GliderWinchItems/BMS/bmsadbms1818/docs/descriptions/header_layout.odt

Note: White bar beside header pin is the GND pin.

1. 4 pin keyed: FAN

2. 3 pin: external LED

3. 2x2: Two spare ADC or I/o

4. 3 pin keyed Molex: DUMP2 FET

5: 4 pin: I2C (gnd,+5, I2C2: SCK, SDA)

6. 6 pin: FTDI (GND, RX, TX)

7. 3 pin: SWD: ST-LINK

8. 2 pin: charger, voltage across 1 ohm

9. 2 pin: thermistor #2: GPIO4 (11/2022 fan control)

10. 2 pin: thermistor #3: GPIO3

11. 2 pin: thermistor #1: GPIO2

12. 3 pin: Hall-effect sensor (gnd, signal: GPIO1, +5)

13. 2 pin: Battery powered (pushbutton for manual wakeup)

14. 2 pin keyed Molex: DUMP (source (black), drain (red))

15. Lug: FET drain (to heater resistor)

16. Lug: FET source (ground)

17. 2 pin: power jumper (remove jumper to measure 12v CAN current)

2x5 header: CAN bus: +12v, -12v, CANH, CANL, Master-Reset)

2x10 header: Battery ribbon

Page 2 11/27/22 BMS1818 header location description
