GliderWinchItems/BMS/docs/description/MAX14921_timing_03182202.PDF

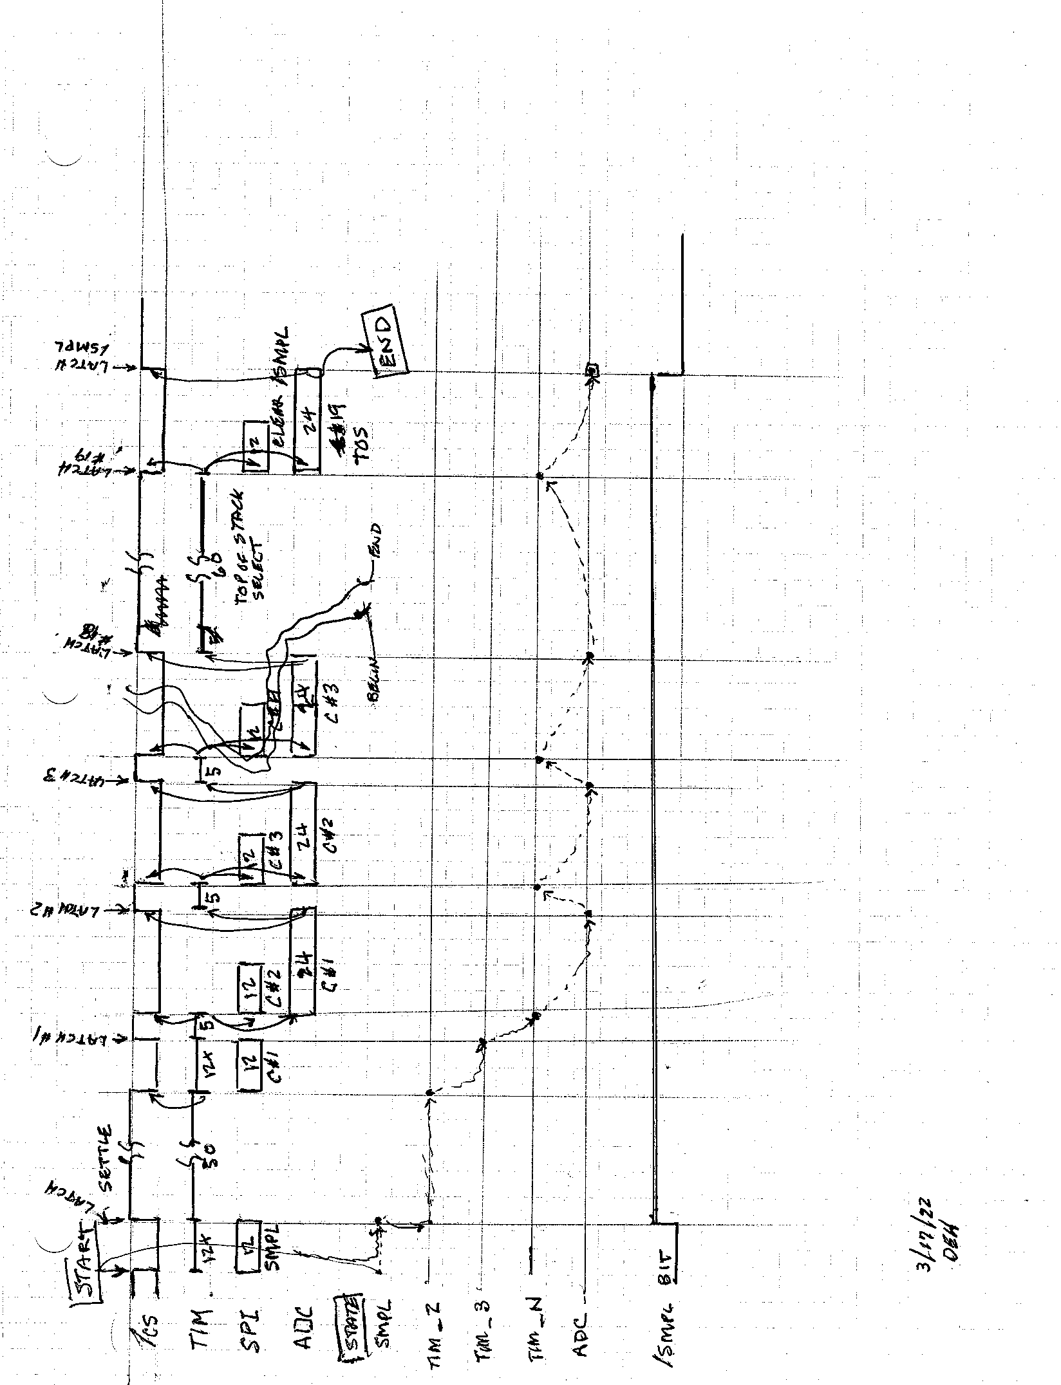
[picture p9: page 1]
