GliderWinchItems/BMS/docs/description/config_02202100.PDF

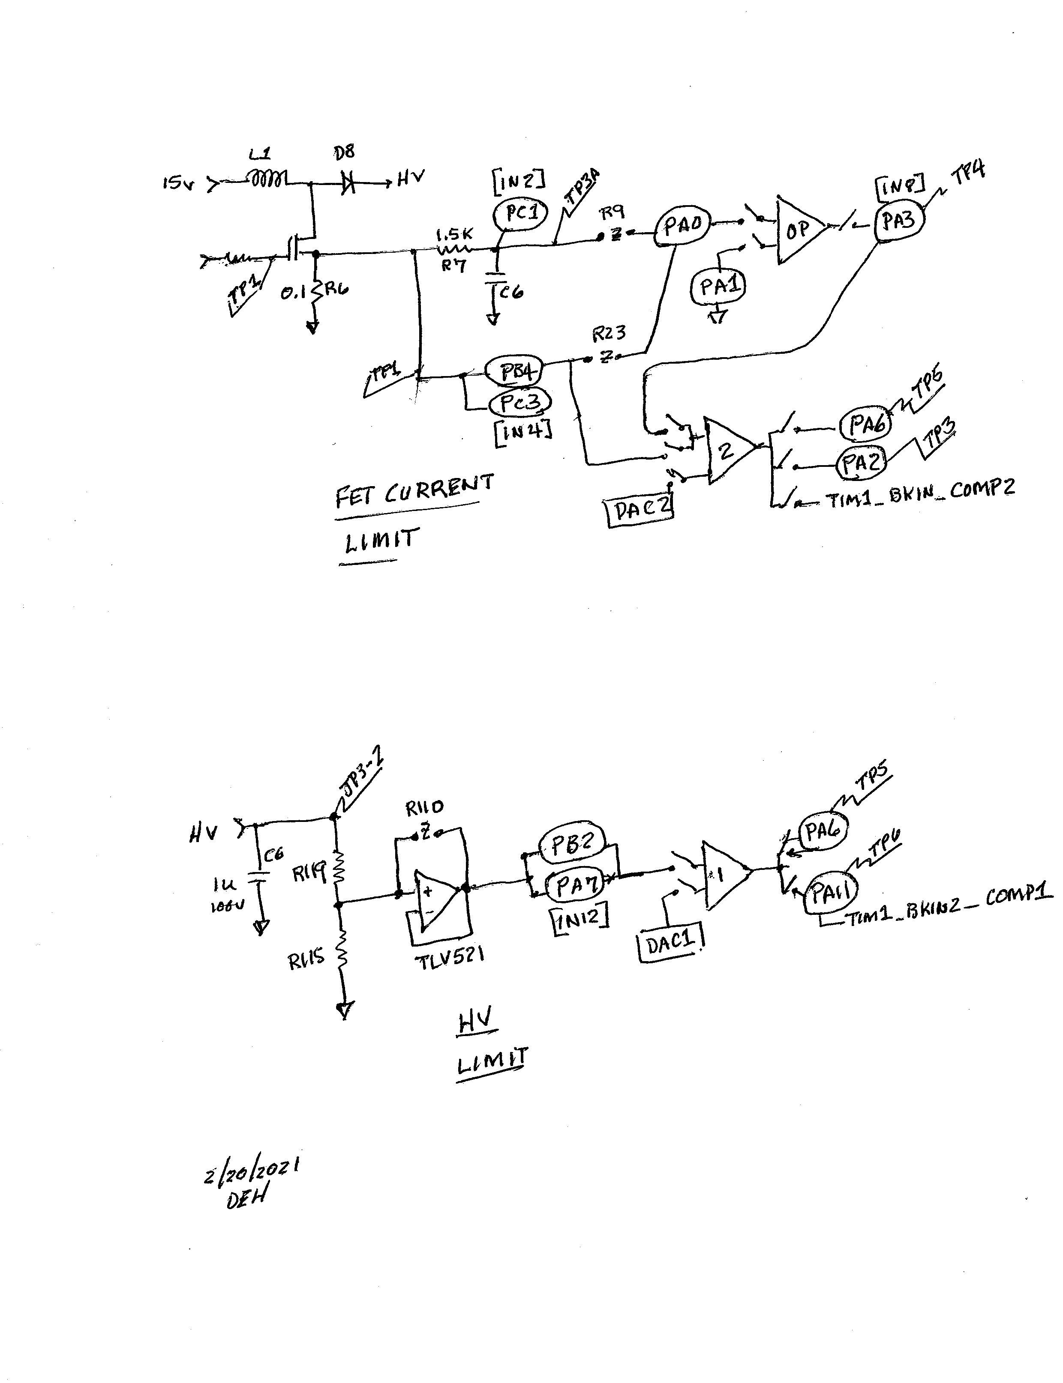
[picture p10: page 1]
