GliderWinchItems/BMS/hw/eagle/bmsbms1818/design_notes.txt

design_notes.txt

06/04/2022

1. Change current sense op amp from GPIO6 to GPIO2

Helps reduce skew for current versus voltage measurements.
See ADCVAX command.

2. '1818 bias resistor 2K-20K.

Use 10K?

08/13/2022

3. Zener vs resistor divider for P-FETs

- Vgs +/- 20v is one solution
- 1M:2M divider
