GliderWinchItems/BMS/LTSpice/BMS_Charger210119.asc

C1: cap; 22µ
C2: cap; 0.1p
C3: cap; 1µ
C4: cap; 6p
D1: schottky; MBRS1100
L1: ind; 47µ; Ipk=2.8 Rser=0.07052 Rpar=4427.4 Cpar=0 mfg="Coilcraft" pn="RFB1010-470"
L2: ind; 1n; Ipk=5 Rser=0.1
M1: nmos; QS8M51_N
R1: res; 500m
R2: res; 50m
R3: res; 10
R4: res; 100m
V1: voltage; 15
V2: voltage; 56
V3: voltage; PULSE(0 5 0 10n 10n 3.4u 7u)
Named nets: 0, Vdrn
.tran 0 224u 210u
