GliderWinchItems/BMS/hw/LTSpice/BMS_Charger.asc

C1: cap; 10µ
C2: cap; 1p
C3: cap; 500n
C4: cap; 18p
D1: schottky; MBRS1100
L1: ind; 39µ; Rser=0.25
L2: ind; 1n; Ipk=5 Rser=0.1
L3: ind; 100n
M1: nmos; QS8M51_N
R1: res; 1
R2: res; 50m
R3: res; 20
R4: res; 100m
R5: res; 5
V1: voltage; 12
V2: voltage; 65
V3: voltage; PULSE(0 5 0 20n 20n 3.5u 5u)
Named nets: 0, Vdrn
.tran 0 100u 75u
