GliderWinchItems/BMS/hw/eagle/Adapt-RJ45to2x5/rj45-2x5.brd

## EAGLE design hw/eagle/Adapt-RJ45to2x5/rj45-2x5.brd (2022-01-06)

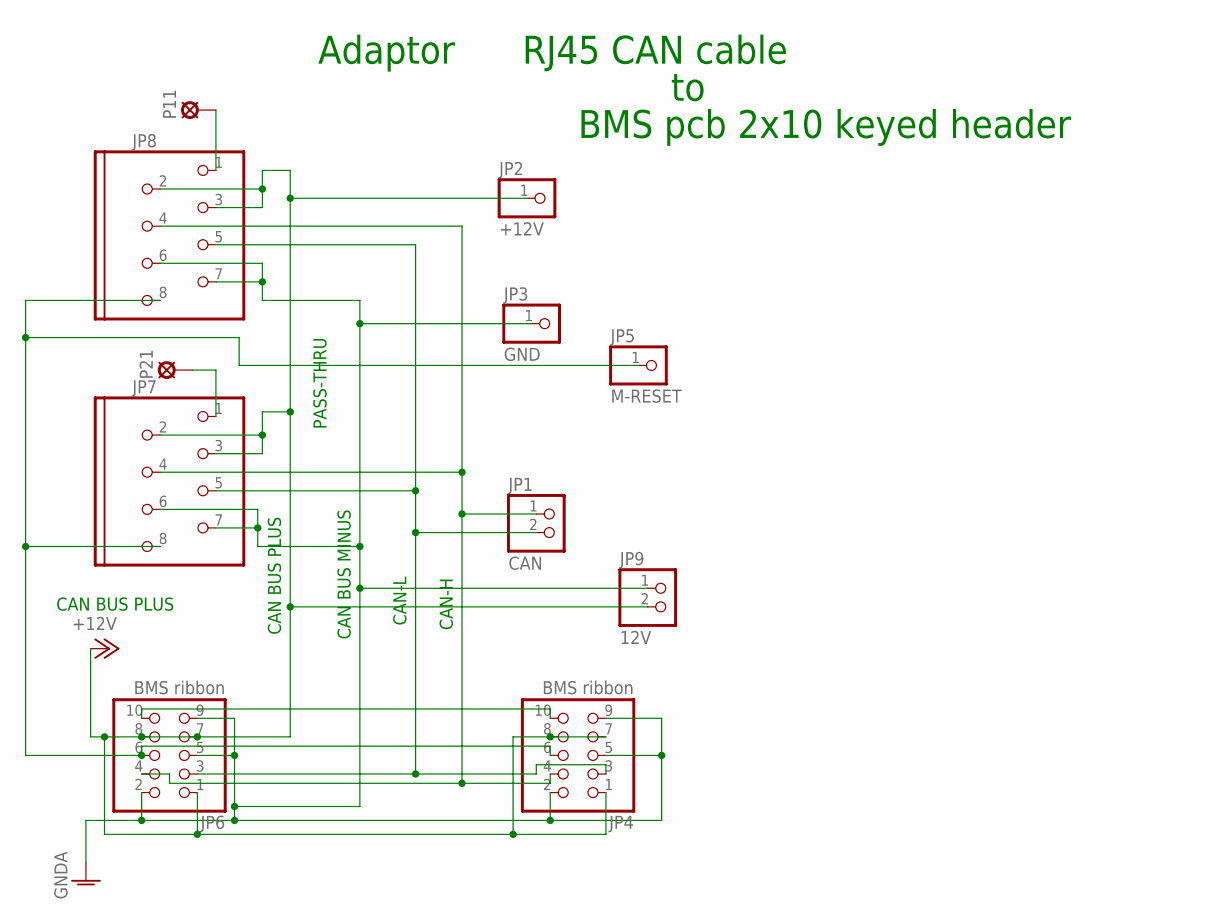
[picture p22: schematic rj45-2x5.sch]

Parts:
JP1: CAN; 1X02
JP2: +12V; 1X01
JP3: GND; 1X01
JP4, JP6: BMS ribbon; 2X05_KEYED
JP5: M-RESET; 1X01
JP7, JP8: MOD8P8C
JP9: 12V; 1X02
P11, P21: SOLPAD035; SOLDPAD035

Connections:
+12V: JP2.1, JP4.1, JP4.7, JP4.8, JP6.1, JP6.7, JP6.8, JP7.2 (5), JP7.3 (2), JP8.2 (5), JP8.3 (2), JP9.2
CANCABLE_1_1: JP8.1, P11.MP
CANCABLE_2_1: JP7.1, P21.MP
CANH: JP1.1, JP4.4, JP6.4, JP7.4 (6), JP8.4 (6)
CANL: JP1.2, JP4.3, JP6.3, JP7.5 (3), JP8.5 (3)
GNDA: JP3.1, JP4.2, JP4.5, JP4.9, JP6.2, JP6.5, JP6.9, JP7.6 (7), JP7.7 (4), JP8.6 (7), JP8.7 (4), JP9.1
MASTER-RESET-SYS: JP4.6, JP5.1, JP6.6, JP7.8, JP8.8
unnamed: JP4.10, JP6.10

Notes on the sheet:
CAN BUS PLUS
PASS-THRU
CAN BUS MINUS
CAN-H
CAN-L
Adaptor
RJ45 CAN cable
BMS pcb 2x10 keyed header

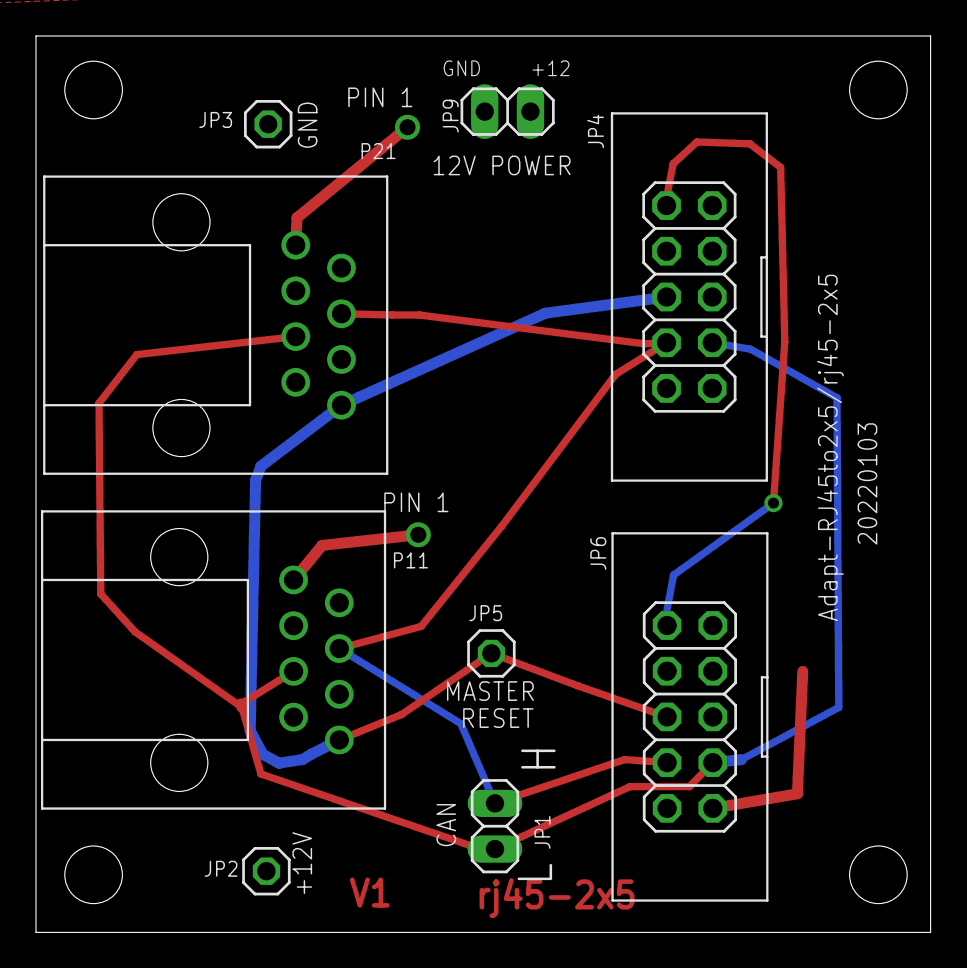
[picture p23: board rj45-2x5.brd from above]

Board: 2 copper layers, 49.7 x 49.8 mm, 11 parts (0 on the bottom side), 8 nets.
