GliderWinchItems/BMS/hw/eagle/rj45-2x10/rj45-2x10.brd

## EAGLE design hw/eagle/rj45-2x10/rj45-2x10.brd (2021-09-04)

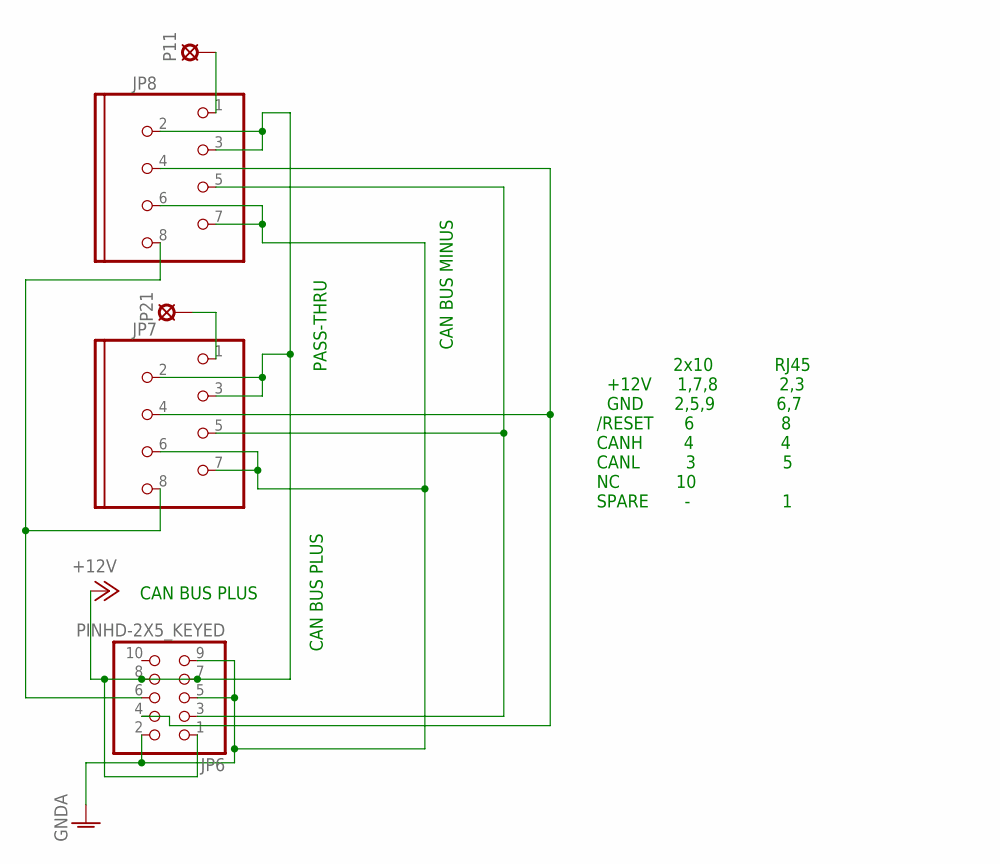
[picture p24: schematic rj45-2x10.sch]

Parts:
JP6: PINHD-2X5_KEYED; 2X05_KEYED
JP7, JP8: MOD8P8C
P11, P21: SOLPAD035; SOLDPAD035

Connections:
+12V: JP6.1, JP6.7, JP6.8, JP7.2 (5), JP7.3 (2), JP8.2 (5), JP8.3 (2)
CANCABLE_1_1: JP8.1, P11.MP
CANCABLE_2_1: JP7.1, P21.MP
CANH: JP6.4, JP7.4 (6), JP8.4 (6)
CANL: JP6.3, JP7.5 (3), JP8.5 (3)
GNDA: JP6.2, JP6.5, JP6.9, JP7.6 (7), JP7.7 (4), JP8.6 (7), JP8.7 (4)
MASTER-RESET-SYS: JP6.6, JP7.8, JP8.8

Notes on the sheet:
CAN BUS PLUS
PASS-THRU
CAN BUS MINUS
2x10 RJ45 +12V 1,7,8 2,3 GND 2,5,9 6,7 /RESET 6 8 CANH 4 4 CANL 3 5 NC 10 SPARE - 1

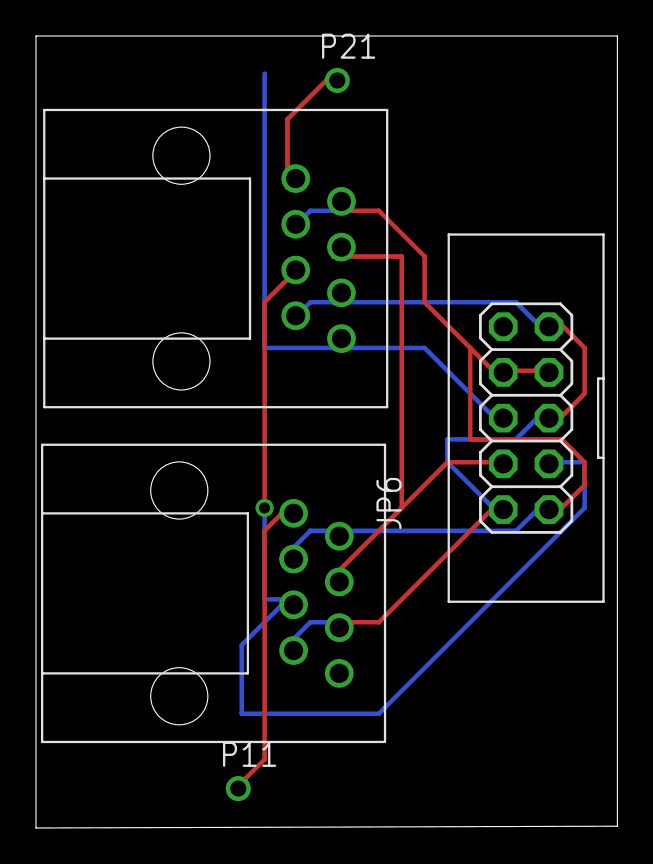
[picture p25: board rj45-2x10.brd from above]

Board: 2 copper layers, 32.3 x 44.0 mm, 5 parts (0 on the bottom side), 7 nets.
