GliderWinchItems/BMS/bmsadbms1818/Core/Inc/main.h

#define RTC_BAT_PWR_Pin GPIO_PIN_13
#define RTC_BAT_PWR_GPIO_Port GPIOC
#define FET_CUR_A2_Pin GPIO_PIN_3
#define FET_CUR_A2_GPIO_Port GPIOC
#define OPAMP_INP_Pin GPIO_PIN_0
#define OPAMP_INP_GPIO_Port GPIOA
#define OPAMP_INM_Pin GPIO_PIN_1
#define OPAMP_INM_GPIO_Port GPIOA
#define OPAMP_OUT_Pin GPIO_PIN_3
#define OPAMP_OUT_GPIO_Port GPIOA
#define dc_dc_15V_Pin GPIO_PIN_4
#define dc_dc_15V_GPIO_Port GPIOA
#define FAN_PWM_Pin GPIO_PIN_5
#define FAN_PWM_GPIO_Port GPIOA
#define HV_div1_Pin GPIO_PIN_7
#define HV_div1_GPIO_Port GPIOA
#define LED_GRN_Pin GPIO_PIN_0
#define LED_GRN_GPIO_Port GPIOB
#define LED_RED_Pin GPIO_PIN_1
#define LED_RED_GPIO_Port GPIOB
#define HV_div2_Pin GPIO_PIN_2
#define HV_div2_GPIO_Port GPIOB
#define FANTach_Pin GPIO_PIN_10
#define FANTach_GPIO_Port GPIOB
#define PADxx_Pin GPIO_PIN_12
#define PADxx_GPIO_Port GPIOB
#define PAD7_Pin GPIO_PIN_15
#define PAD7_GPIO_Port GPIOB
#define DUMP2_Pin GPIO_PIN_6
#define DUMP2_GPIO_Port GPIOC
#define DUMP_NOT_Pin GPIO_PIN_8
#define DUMP_NOT_GPIO_Port GPIOC
#define CSB_Pin GPIO_PIN_15
#define CSB_GPIO_Port GPIOA
#define DUMP_Pin GPIO_PIN_10
#define DUMP_GPIO_Port GPIOC
#define HEATER_NOT_Pin GPIO_PIN_11
#define HEATER_NOT_GPIO_Port GPIOC
#define HEATER_Pin GPIO_PIN_12
#define HEATER_GPIO_Port GPIOC
#define BQ_LD_Pin GPIO_PIN_2
#define BQ_LD_GPIO_Port GPIOD
#define WDT_Pin GPIO_PIN_7
#define WDT_GPIO_Port GPIOB
#define WDT_EXTI_IRQn EXTI9_5_IRQn
#define HUARTMON  huart1 // uart  for PC monitoring
#define DEFAULTTASKBIT00 (1 << 0)  // Task notification bit (from ADCtask.c)
#define DEFAULTTASKBIT01 (1 << 1)  // Task notification bit (from BQtask.c)
#define DEFAULTTASKBIT02 (1 << 2)  // Task notification bit (from Mailbox)
#define MAINFORLOOPDELAY 50 // main.c Delay of 'for' loop (ms)
