GliderWinchItems/BMS/bmsmax14921/Ourtasks/CanCommTask.c

/******************************************************************************
* File Name          : CanCommTask.c
* Date First Issued  : 11/06/2021
* Description        : Can communications
*******************************************************************************/

#include "FreeRTOS.h"
#include "task.h"
#include "cmsis_os.h"
#include "malloc.h"

#include "main.h"
#include "morse.h"
#include "CanCommTask.h"
#include "MailboxTask.h"
#include "CanTask.h"
#include "can_iface.h"
#include "canfilter_setup.h"
#include "BQTask.h"
#include "cancomm_items.h"
#include "../../../../GliderWinchCommons/embed/svn_common/trunk/db/gen_db.h"

extern struct CAN_CTLBLOCK* pctl0; // Pointer to CAN1 control block
extern CAN_HandleTypeDef hcan1;

static void canfilt(uint16_t mm, struct MAILBOXCAN* p);

#define CANCOMMBIT00 (1 << 0) // Send cell voltage  command
#define CANCOMMBIT01 (1 << 1) // Send misc reading command
#define CANCOMMBIT02 (1 << 2) // Multi-purpose incoming command
#define CANCOMMBIT03 (1 << 3) // ADCTask completed BMS read 

struct CANRCVBUF  can_hb; // Dummy heart-beat request CAN msg
uint8_t hbseq; // heartbeat CAN msg sequence number
uint8_t rdyflag_cancomm = 0; // Initialization complete and ready = 1

TaskHandle_t CanCommHandle = NULL;

static struct ADCREADREQ adcreadreq; // Request BMS readout

uint8_t dbupdnx;

/* Walking discharge FETs for testing. */
uint16_t dbdischargectr; // hb counter for timing
uint8_t  dbdischargebit; // Discharge bit (0-15)

/* Arrays loaded by readbms. */
float fbms[ADCBMSMAX]; // (16+3+1) = 20; Number of MAX14921 (cells+thermistors+tos)   
uint16_t uibms[ADCBMSMAX];

/* *************************************************************************
 * void CanComm_init(struct BQFUNCTION* p );
 *	@brief	: Task startup
 * *************************************************************************/
void CanComm_init(struct BQFUNCTION* p )
{
	uint8_t i;

	/* Add CAN Mailboxes                               CAN     CAN ID             TaskHandle,Notify bit,Skip, Paytype */
    p->pmbx_cid_cmd_bms_cellvq = MailboxTask_add(pctl0,p->lc.cid_cmd_bms_cellvq, NULL, CANCOMMBIT00,0,U8); // Command: send cell voltages
    if (p->pmbx_cid_cmd_bms_cellvq == NULL) morse_trap(620);
    p->pmbx_cid_cmd_bms_miscq  = MailboxTask_add(pctl0,p->lc.cid_cmd_bms_miscq,  NULL, CANCOMMBIT01,0,U8); // Command: many options	
    if (p->pmbx_cid_cmd_bms_miscq == NULL) morse_trap(621);
    p->pmbx_cid_uni_bms_i      = MailboxTask_add(pctl0,p->lc.cid_uni_bms_i,      NULL, CANCOMMBIT02,0,U8); // muli-purpose BQ76952  #01
    if (p->pmbx_cid_uni_bms_i == NULL) morse_trap(622);

    /* Add CAN msgs to incoming CAN filter. */
 //   canfilt(601, p->pmbx_cid_cmd_bms_cellvq);
 //   canfilt(602, p->pmbx_cid_cmd_bms_miscq);
 //   canfilt(603, p->pmbx_cid_uni_bms_i);

    	/* Pre-load fixed data in all possible CAN msgs */
	for (i = 0; i < NUMCANMSGS; i++)
	{
		p->canmsg[i].pctl = pctl0;   // Control block for CAN module (CAN 1)
		p->canmsg[i].maxretryct = 4; //
		p->canmsg[i].bits = 0;       //
		p->canmsg[i].can.dlc = 8;    // Default payload size (might be modified when loaded and sent)
	}

	/* Preload fixed data for sending cell reading msgs. */
	for (i = 0; i < MAXNUMCELLMSGS; i++)
	{	
		/* Preload CAN IDs */
		p->canmsg[CID_MSG_CELLV01 + i].can.id = p->lc.cid_msg_bms_cellvsmr;

		/* Msg identification = cell readings. */
		p->canmsg[CID_MSG_CELLV01 + i].can.cd.ui[0]  = CMD_CMD_TYPE1;//

		/* Preload cell_number-1 for first payload in cell reading msg. */
		// 0,3,6,9,12,15 in upper nibble; lower order nibble (seq number) = 0;
		p->canmsg[CID_MSG_CELLV01 + i].can.cd.ui[1] = ((i*3) << 4); 
	}

	/* Preload fixed data for sending "misc" readings. */
	p->canmsg[CID_CMD_MISC].can.id = p->lc.cid_msg_bms_cellvsmr;
	p->canmsg[CID_CMD_MISC].can.cd.uc[2] = p->ident_onlyus;

	/* Pre-load a dummy CAN msg request for sending heartbeat CAN msg. */
	can_hb.id       = p->lc.cid_uni_bms_i;
	can_hb.cd.ull   = 0; // Clear entire payload
	can_hb.cd.uc[0] = CMD_CMD_TYPE1;  // request code (initial, changed later)
	can_hb.cd.uc[4] = p->lc.cid_msg_bms_cellvsmr >>  0; // Our CAN ID
	can_hb.cd.uc[5] = p->lc.cid_msg_bms_cellvsmr >>  8;
	can_hb.cd.uc[6] = p->lc.cid_msg_bms_cellvsmr >> 16;
	can_hb.cd.uc[7] = p->lc.cid_msg_bms_cellvsmr >> 24;

	return;
}

/* *************************************************************************
 * void StartCanComm(void const * argument);
 *	@brief	: Task startup
 * *************************************************************************/
void StartCanComm(void* argument)
{
//while(1==1) osDelay(100);

	BaseType_t qret;
	uint32_t noteval2;
	struct ADCREADREQ* padcreadreq = &adcreadreq;

	/* We use the parameters from BQ for this task. */
	struct BQFUNCTION* p = &bqfunction;
	struct CANRCVBUF* pcan;

	uint32_t doneflagctr;

	/* A notification copies the internal notification word to this. */
	uint32_t noteval = 0;    // Receives notification word upon an API notify
	uint32_t timeoutwait;
	uint8_t intadj = 0;
	uint8_t code;

//	while (CANTaskreadyflag == 0) osDelay(1); // Debug

	/* Pre-load BMS readout request queue block. */	
//	adcreadreq.taskhandle = CanCommHandle; // Requesting task's handle
//	adcreadreq.tasknote   = CANCOMMBIT03;  // ADCTask completed BMS read 
	adcreadreq.taskdata   = &fbms[0];  // Requesting task's pointer to buffer to receive data
	adcreadreq.taskdatai16= &uibms[0]; // Requesting task's pointer to int16_t buffer to receive data
	adcreadreq.cellbits   = 0x0000;    // Depends on command: FET to set; Open cell wires
	adcreadreq.updn       = 0; // BMS readout direction 0 = high->low cell numbers; 1 = low->high
	adcreadreq.reqcode    = REQ_READBMS;  // Read MAX1921 cells, thermistor, Top-of-stack
	adcreadreq.encycle    = 1;     // Cycle EN: 0 = after read; 1 = before read w osDelay; 2 = neither
	adcreadreq.readbmsfets= 0;        // Clear discharge fets before readbms.	
	adcreadreq.doneflag   = 0; // 1 = ADCTask completed BMS read 
dbupdnx = adcreadreq.updn;

	/* CAN communications parameter init. */
	CanComm_init(p);

	extern CAN_HandleTypeDef hcan1;
	HAL_CAN_Start(&hcan1); // CAN1

	rdyflag_cancomm = 1; // Initialization complete and ready
/* ******************************************************************* */
	for (;;)
	{
		/* Wait for notifications */
		/* Do exactly 12 timeouts per second. */
		intadj += 1;
		if (intadj >= 3)
		{
			timeoutwait = 84;
			intadj = 0;
		}
		else
		{
			timeoutwait = 83;
		}
//timeoutwait = 40;

		xTaskNotifyWait(0,0xffffffff, &noteval,timeoutwait);

		/* Read BMS cells. */
		adcreadreq.doneflag   = 0;
		doneflagctr = 0;

		qret = xQueueSendToBack(ADCTaskReadReqQHandle, &padcreadreq, 5000);
if (qret != pdPASS) morse_trap(720); // JIC debug

		/* Wait for ADCTask to complete request. */
#define DONEFLAGCT 200
		while ((adcreadreq.doneflag == 0) && (doneflagctr++ < DONEFLAGCT)) 
			osDelay(1);
		if (doneflagctr >= DONEFLAGCT) morse_trap(731);


		/* Filter readings for calibration purposes. */
		cancomm_items_filter(pssb->taskdatai16); // Filter 	

/* ******* CAN msg request for sending CELL VOLTAGES. */
			// Code for which modules should respond bits [7:6]
	   		// 11 = All modules respond
       		// 10 = All modules on identified string respond
       		// 01 = Only identified string and module responds
       		// 00 = spare; no response expected
		if ((noteval & CANCOMMBIT00) != 0) // cid_cmd_bms_cellvq
		{
morse_trap(6666);			
			pcan = &p->pmbx_cid_cmd_bms_cellvq->ncan.can;
			code = pcan->cd.uc[0] & 0xC0; // Extract identification code
			if (((code == (3 << 6))) ||
				((code == (2 << 6)) && ((pcan->cd.uc[0] & 0x30) == p->ident_string)) ||
				((code == (1 << 6)) && ((pcan->cd.uc[0] & 0x3F) == p->ident_onlyus)) )
			{ // Here, respond to request, otherwise, ignore.
				qret = xQueueSendToBack(ADCTaskReadReqQHandle, &padcreadreq, 5000);
				if (qret != pdPASS) morse_trap(726); // JIC debug

				/* Wait for ADCTask to signal request complete. */
				xTaskNotifyWait(0,0xffffffff, &noteval2, 5000);
				if (noteval2 != CANCOMMBIT03) morse_trap(727); // JIC debug

				cancomm_items_uni_bms(&can_hb, &fbms[0]);
			}
		}
/* ******* CAN msg request for sending MISC READINGS. */
			// Code for which modules should respond bits [7:6]
	   		// 11 = All modules respond
       		// 10 = All modules on identified string respond
       		// 01 = Only identified string and module responds
       		// 00 = spare; no response expected
		if ((noteval & CANCOMMBIT01) != 0) // cid_cmd_bms_miscq
		{
morse_trap(5555);
			pcan = &p->pmbx_cid_cmd_bms_miscq->ncan.can;
			code = pcan->cd.uc[0] & 0xC0; // Extract identification code
			if (((code == (3 << 6))) ||
				((code == (2 << 6)) && ((pcan->cd.uc[0] & 0x30) == p->ident_string)) ||
				((code == (1 << 6)) && ((pcan->cd.uc[0] & 0x3F) == p->ident_onlyus)) )
			{ // Here, respond to request
				cancomm_items_sendcmdr(pcan);
			}
		}
/* ******* CAN msg request for sending MISC READINGS. */
		if ((noteval & CANCOMMBIT02) != 0) // cid_uni_bms_i
		{
bqfunction.CanComm_hb_ctr = 0;			
			cancomm_items_uni_bms(&p->pmbx_cid_uni_bms_i->ncan.can, NULL);
		}

/* ******* Timeout notification. */
		if (noteval == 0)
		{ // Send heartbeat

#if 0 /* Walk discharge FETs for testing. */
			dbdischargectr += 1; // Time delay counter
			if (dbdischargectr >= 32)
			{ // Set FETs off
				adcreadreq.cellbits = 0;
			}
			if (dbdischargectr >= 64)
			{ // Step to next FET
				dbdischargectr = 0;
				dbdischargebit += 1;
				if (dbdischargebit >= 16) dbdischargebit = 0;
			}
#endif
			/* Here, 12 times per second. Slow down for heartbeat. */
			bqfunction.CanComm_hb_ctr += 1;
			if (bqfunction.CanComm_hb_ctr >= bqfunction.lc.CanComm_hb)
			{
				bqfunction.CanComm_hb_ctr = 0;

				/* Use dummy CAN msg, then it looks the same as a request CAN msg. */
				can_hb.cd.uc[0] = CMD_CMD_TYPE2;  // Misc subcommands code
				can_hb.cd.uc[1] = MISCQ_STATUS;   // status code
				cancomm_items_uni_bms(&can_hb,&bqfunction.cal_filt[0]); // filtered

				/* Use dummy CAN msg, then it looks the same as a request CAN msg. */
				can_hb.cd.uc[0] = CMD_CMD_TYPE1;  // cell readings code
				can_hb.cd.uc[1] = (hbseq & 0x0f); // Group sequence number
				cancomm_items_uni_bms(&can_hb, &bqfunction.cal_filt[0]); // filtered

				/* Increment 4 bit CAN msg group sequence counter .*/
				hbseq += 1;
//	   			xQueueSendToBack(CanTxQHandle,&p->canmsg[CID_CMD_MISC],4);   
   			}
		}	
	} 	
}

/* *************************************************************************
 * TaskHandle_t xCanCommCreate(uint32_t taskpriority);
 * @brief	: Create task; task handle created is global for all to enjoy!
 * @param	: taskpriority = Task priority (just as it says!)
 * @return	: CanCommHandle
 * *************************************************************************/
TaskHandle_t xCanCommCreate(uint32_t taskpriority)
{
	BaseType_t ret = xTaskCreate(StartCanComm, "CanComm",\
     (128), NULL, taskpriority,\
     &CanCommHandle);
	if (ret != pdPASS) return NULL;

	return CanCommHandle;
}
/* *************************************************************************
 * static void canfilt(uint16_t mm, struct MAILBOXCAN* p);
 * @brief	: Setup CAN hardware filter with CAN addresses to receive
 * @param	: p    = pointer to ContactorTask
 * @param   : mm = morse_trap numeric number
 * *************************************************************************/
static void canfilt(uint16_t mm, struct MAILBOXCAN* p)
{
/*	HAL_StatusTypeDef canfilter_setup_add32b_id(uint8_t cannum, CAN_HandleTypeDef *phcan, \
    uint32_t id,   \
    uint8_t  fifo );
 @brief	: Add a 32b id, advance bank number & odd/even
 * @param	: cannum = CAN module number 1, 2, or 3
 * @param	: phcan = Pointer to HAL CAN handle (control block)
 * @param	: id    = 32b CAN id
 * @param	: fifo  = fifo: 0 or 1
 * @return	: HAL_ERROR or HAL_OK
*/
	HAL_StatusTypeDef ret;	
	ret = canfilter_setup_add32b_id(1,&hcan1,p->ncan.can.id,0);
	if (ret == HAL_ERROR) morse_trap(mm);	
	return;
}
