GliderWinchItems/BMS/bmsadbms1818/params/B0A00000-bq_idx_v_struct.c

/******************************************************************************
* File Name          : B0A00000-bq_idx_v_struct.c
* Date First Issued  : 08/20/2022
* Board              : bmsadbms1818
* Description        : Load BQ parameter struct: B0A00000 ADBMS1818 board #1
*******************************************************************************/
/*
16 pin CAN ISO1042
*/

#include "bq_idx_v_struct.h"
#include "SerialTaskReceive.h"
#include "morse.h"
#include "../../../../GliderWinchCommons/embed/svn_common/trunk/db/gen_db.h"

/* *************************************************************************
 * void bq_idx_v_struct_hardcode_params(truct BQLC* p);
 * @brief	: Init struct from hard-coded parameters (rather than database params in highflash)
 * @return	: 0
 * *************************************************************************/
void bq_idx_v_struct_hardcode_params(struct BQLC* p)
{
   p->size    = 32;
   p->crc     = 0;   // TBD
   p->version = 1;   // 

   /* Timings in milliseconds. Converted later to timer ticks. */

   /* Identification of this module node. */
   p->winchnum     = 1; // Winch number (1 - 4)
   if ((p->winchnum == 0) || (p->winchnum > 4)) morse_trap(700);
   p->stringnum    = 1; // Battery string number (1 - 4)
   if ((p->stringnum == 0) || (p->stringnum > 4)) morse_trap(701);
   p->modulenum    = 2; // Module number on string (1-16)
   if ((p->modulenum == 0) || (p->modulenum > 16)) morse_trap(702);

   p->hbct_t       = 4000; // Heartbeat ct: milliseconds between sending 
   p->hbct         = 64;    // Number of swctr ticks between heartbeats
//   p->adc_hb       = 64;     // Number of ticks for heartbeat ADC readout

   p->CanComm_hb = 1000; // CanCommTask 'wait' RTOS ticks per heartbeat sending
 
   p->dcdc_v    = 15.0; // Isolated DC-DC converter output voltage (e.g. 15.0v)
   p->dcdc_w    =  5.2; // Charger power max taken from DC-DC converter (e.g. 5.5W)
   p->dcdc_calv = 68.5; // Module voltage used in following settings (e.g. 57.6v)

   /* Charger: timer and comparator settings. */
   p->dac1_hv_setting  = 3900; // HV volt limit (DAC setting, not mv!)
   p->dac2_ix_setting  =   85; // Current sense level setting (DAC setting)
   p->tim1_ccr1_on     =  999; // PWM ON count: Normal charge rate
   p->tim1_ccr1_on_vlc =   10; // PWM ON count: Very Low Charge rate required
   p->tim1_arr_init    =   25; // At 16 MHz: count of 80 = 5 us PWM frame

   p->cellv_max      = 3750; // Max limit (mv) for charging any cell
   p->cellv_min      = 2800; // Min limit (mv) for any discharging
   p->cellv_vlc      = 2100; // Below this (mv) Very Low Charge (vlc)required
   p->cellv_tgtdelta =    3; // Target delta (mv)   
   p->cellopen_hi    = 4000; // Above this voltage cell wire is assumed open (mv)
   p->cellopen_lo    =  333; // Below this voltage cell wire is assumed open (mv)
   p->cellv_max2_inc =  100; // Increment added to cellv_max for external charging

   p->balnummax    = 18;  // Max number of cells to discharge at one time

   // Voltage below cellv_max to start recharging (mv)
   p->cellv_hyster = (p->cellv_max - 3250);  // 3250 LFP ~50% charge

   p->dumpresistor = 450; // DUMP fet load resistor (Ohms)

   /* Future Not implemented (09/13/23) */
   p->cellv_launch_ng  = 3144;  //  Low cell voltage for launch no-go (mv)
   p->cellv_min_loaded = 1800;  //  Low cell voltage too low even under load (mv)

   p->cellbal_del  = 2; // Legacy

  /* Arrays compiled using NCELLMAX [18] */
   p->ncell = 18; // Number of series cells in this module
   if (p->ncell > NCELLMAX) morse_trap(702); // Error trap as it needs fixing
   p->npositions  = 18;  // Number of cell =>positions<= in module "box"

   p->modulev_max = (p->ncell*p->cellv_max); // Battery module max limit (mv)
   p->modulev_min = (p->ncell*p->cellv_min); // Battery module min limit (mv)

   /* These are sent to the EMC for module level charging control. */
   p->maxchrgcurrent  = 13; // Maximum charge current (0.1a) (over 25.5a = 255)
   p->chrgcurrent_bal = 2; // Charge current for module balancing (0.1a)
   p->maxmodule_v     = (p->modulev_max/100);  // module voltage limit (0.1v)      

   /* Relate cell numbers to cell positions. (indices are ("number"-1) */
#define EighteenPositionBox
  #define EighteenCellsInEighteenBox
   
#ifdef EighteenPositionBox

 #ifdef EighteenCellsInEighteenBox
   /* 18 cells installed in 18 position box. */
   p->cellpos[ 0]  =  0; // Cell #1 installed in cell position #1
   p->cellpos[ 1]  =  1; // ...
   p->cellpos[ 2]  =  2; // 
   p->cellpos[ 3]  =  3; // 
   p->cellpos[ 4]  =  4; // 
   p->cellpos[ 5]  =  5; // 
   p->cellpos[ 6]  =  6; // 
   p->cellpos[ 7]  =  7; // 
   p->cellpos[ 8]  =  8; 
   p->cellpos[ 9]  =  9;
   p->cellpos[10]  = 10; 
   p->cellpos[11]  = 11; 
   p->cellpos[12]  = 12; 
   p->cellpos[13]  = 13; 
   p->cellpos[14]  = 14; 
   p->cellpos[15]  = 15; 
   p->cellpos[16]  = 16; 
   p->cellpos[17]  = 17; // Cell #18 is installed in cell position #18

 #else  
   /* 16 cells installed in 18 position box. */
   p->cellpos[ 0]  =  0; // Cell #1 installed in cell position #1
   p->cellpos[ 1]  =  1; // ...
   p->cellpos[ 2]  =  2; // 
   p->cellpos[ 3]  =  3; // 
   p->cellpos[ 4]  =  4; // 
   p->cellpos[ 5]  =  5; // 
   p->cellpos[ 6]  =  6; // 
   p->cellpos[ 7]  =  7; // Cell #8 is installed in cell position #8
   p->cellpos[ 8]  =  CELLNONE; // No cell in cell position 8
   p->cellpos[ 9]  =  CELLNONE; // No cell in cell position 9
   p->cellpos[10]  =  8; // Cell #9 is installed in cell position 10
   p->cellpos[11]  =  9; // ...
   p->cellpos[12]  = 10; 
   p->cellpos[13]  = 11; 
   p->cellpos[14]  = 12; 
   p->cellpos[15]  = 13; 
   p->cellpos[16]  = 14; 
   p->cellpos[17]  = 15; // Cell #16 is installed in cell position #18
 #endif

#else

     /* 16 cells installed in 16 position box, or 18 position box wired as such. */
   p->cellpos[ 0]  =  0; // Cell #1 installed in cell position #1
   p->cellpos[ 1]  =  1; // ...
   p->cellpos[ 2]  =  2; // 
   p->cellpos[ 3]  =  3; // 
   p->cellpos[ 4]  =  4; // 
   p->cellpos[ 5]  =  5; // 
   p->cellpos[ 6]  =  6; // 
   p->cellpos[ 7]  =  7; //
   p->cellpos[ 8]  =  8; // 
   p->cellpos[ 9]  =  9; // 
   p->cellpos[10]  = 10; // 
   p->cellpos[11]  = 11; // 
   p->cellpos[12]  = 12; //
   p->cellpos[13]  = 13; //
   p->cellpos[14]  = 14; //
   p->cellpos[15]  = 15; // Cell #16 installed in cell position #16
   p->cellpos[16]  = CELLNONE; // No cell
   p->cellpos[17]  = CELLNONE; // No cell

#endif

   /* Cell # 1 */
   p->bmscal[ 0].coef[0] = 0;
   p->bmscal[ 0].coef[1] = 1;
   p->bmscal[ 0].coef[2] = 0;

   /* Cell # 2 */
   p->bmscal[ 1].coef[0] = 0;
   p->bmscal[ 1].coef[1] = 1;
   p->bmscal[ 1].coef[2] = 0;

   /* Cell # 3 */
   p->bmscal[ 2].coef[0] = 0;
   p->bmscal[ 2].coef[1] = 1;
   p->bmscal[ 2].coef[2] = 0;

   /* Cell # 4 */
   p->bmscal[ 3].coef[0] = 0;
   p->bmscal[ 3].coef[1] = 1;
   p->bmscal[ 3].coef[2] = 0;

   /* Cell # 5 */
   p->bmscal[ 4].coef[0] = 0;
   p->bmscal[ 4].coef[1] = 1;
   p->bmscal[ 4].coef[2] = 0;

   /* Cell # 6 */
   p->bmscal[ 5].coef[0] = 0;
   p->bmscal[ 5].coef[1] = 1;
   p->bmscal[ 5].coef[2] = 0;

   /* Cell # 7 */
   p->bmscal[ 6].coef[0] = 0;
   p->bmscal[ 6].coef[1] = 1;
   p->bmscal[ 6].coef[2] = 0;

   /* Cell # 8 */
   p->bmscal[ 7].coef[0] = 0;
   p->bmscal[ 7].coef[1] = 1;
   p->bmscal[ 7].coef[2] = 0;

   /* Cell # 9 */
   p->bmscal[ 8].coef[0] = 0;
   p->bmscal[ 8].coef[1] = 1;
   p->bmscal[ 8].coef[2] = 0;

   /* Cell #10 */
   p->bmscal[ 9].coef[0] = 0;
   p->bmscal[ 9].coef[1] = 1;
   p->bmscal[ 9].coef[2] = 0;

   /* Cell #11 */
   p->bmscal[10].coef[0] = 0;
   p->bmscal[10].coef[1] = 1;
   p->bmscal[10].coef[2] = 0;

   /* Cell #12 */
   p->bmscal[11].coef[0] = 0;
   p->bmscal[11].coef[1] = 1;
   p->bmscal[11].coef[2] = 0;

   /* Cell #13 */
   p->bmscal[12].coef[0] = 0;
   p->bmscal[12].coef[1] = 1;
   p->bmscal[12].coef[2] = 0;

   /* Cell #14 */
   p->bmscal[13].coef[0] = 0;
   p->bmscal[13].coef[1] = 1;
   p->bmscal[13].coef[2] = 0;

   /* Cell #15 */
   p->bmscal[14].coef[0] = 0;
   p->bmscal[14].coef[1] = 1;
   p->bmscal[14].coef[2] = 0;

   /* Cell #16 */
   p->bmscal[15].coef[0] = 0;
   p->bmscal[15].coef[1] = 1;
   p->bmscal[15].coef[2] = 0;

   /* Cell #17 */
   p->bmscal[16].coef[0] = 0;
   p->bmscal[16].coef[1] = 1;
   p->bmscal[16].coef[2] = 0;

   /* Cell #18 */
   p->bmscal[17].coef[0] = 0;
   p->bmscal[17].coef[1] = 1;
   p->bmscal[17].coef[2] = 0;

   /* Initialize iir filter. */
   #define CELLTC 0.70f // Default filter time constant
   for (int i = 0; i < NCELLMAX; i++)
   {
      p->bmscal[i].iir_f1.coef = CELLTC; // Initialize all to the same
   }
   /* === Insert non-default filter coefficients here. === */
   for (int i = 0; i < NCELLMAX; i++)
   {
      p->bmscal[i].iir_f1.onemcoef = 1 - p->bmscal[i].iir_f1.coef;
   }


   /* Auxilarly GPIO 1 Hall-effect  */
   // NOTE: 10K pull-up installed at board header underside
   p->bmsaux[BMSAUX_1_NC].coef[0] = 25004;
   p->bmsaux[BMSAUX_1_NC].coef[1] = 5.24E-4f;;
   p->bmsaux[BMSAUX_1_NC].coef[2] = 0;

   /* Auxilarly GPIO 2 Thermistor 1 */
   p->bmsaux[BMSAUX_2_THERM1].coef[0] = 0;
   p->bmsaux[BMSAUX_2_THERM1].coef[1] = 1;
   p->bmsaux[BMSAUX_2_THERM1].coef[2] = 0;

   /* Auxilarly GPIO 3 Thermistor 3 */
   p->bmsaux[BMSAUX_3_THERM3].coef[0] = 0;
   p->bmsaux[BMSAUX_3_THERM3].coef[1] = 1;
   p->bmsaux[BMSAUX_3_THERM3].coef[2] = 0;

   /* Auxilarly GPIO 4 Thermistor 2 */
   p->bmsaux[BMSAUX_4_THERM2].coef[0] = 0;
   p->bmsaux[BMSAUX_4_THERM2].coef[1] = 1;
   p->bmsaux[BMSAUX_4_THERM2].coef[2] = 0;

   /* Auxilarly GPIO 5 Spare: U$6 */
   p->bmsaux[BMSAUX_5_US5].coef[0] = 0;
   p->bmsaux[BMSAUX_5_US5].coef[1] = 1;
   p->bmsaux[BMSAUX_5_US5].coef[2] = 0;

   /* Auxilarly REF */
   p->bmsaux[BMSAUX_REF].coef[0] = 0;
   p->bmsaux[BMSAUX_REF].coef[1] = 1;
   p->bmsaux[BMSAUX_REF].coef[2] = 0;

   /* Auxilarly GPIO 6 Current sense op amp */
   p->bmsaux[BMSAUX_6_CUR_SENSE].coef[0] = 27569.0f;
   p->bmsaux[BMSAUX_6_CUR_SENSE].coef[1] = 9.03E-02f;
   p->bmsaux[BMSAUX_6_CUR_SENSE].coef[2] = 0;

   /* Auxilarly GPIO 7 U$12 w divider */
   p->bmsaux[BMSAUX_7_HALL].coef[0] = 0;
   p->bmsaux[BMSAUX_7_HALL].coef[1] = 1;
   p->bmsaux[BMSAUX_7_HALL].coef[2] = 0;

   /* Auxilarly GPIO 8 Spare: U$9 */
   p->bmsaux[BMSAUX_8_US9].coef[0] = 0;
   p->bmsaux[BMSAUX_8_US9].coef[1] = 1;
   p->bmsaux[BMSAUX_8_US9].coef[2] = 0;

   /* Auxilarly GPIO 9 Spare: U$10 */
   p->bmsaux[BMSAUX_9_US10].coef[0] = 0;
   p->bmsaux[BMSAUX_9_US10].coef[1] = 1;
   p->bmsaux[BMSAUX_9_US10].coef[2] = 0;

     /* Initialize iir filter. */
   #define AUXTC 0.70f // Default filter time constant
   for (int i = 0; i < NAUXMAX; i++)
   {
      p->bmscal[i].iir_f1.coef = AUXTC; // Initialize all to the same
   }
   /* === Insert non-default filter coefficients here. === */
   for (int i = 0; i < NAUXMAX; i++)
   {
      p->bmscal[i].iir_f1.onemcoef = 1 - p->bmscal[i].iir_f1.coef;
   }

// Thermisters: calibration & results
   p->thermcal[0].tt[0] = 100.81f; 
   p->thermcal[0].tt[1] = -3.85E-3f;
   p->thermcal[0].tt[2] = 2.99E-8f;

   p->thermcal[1].tt[0] = 100.81f; 
   p->thermcal[1].tt[1] = -3.85E-3f;
   p->thermcal[1].tt[2] = 2.99E-8f;

   p->thermcal[2].tt[0] = 100.81f; 
   p->thermcal[2].tt[1] = -3.85E-3f;
   p->thermcal[2].tt[2] = 2.99E-8f;

   /* Overall max temperature threshold. (deg C) */
   p->thermcal[0].max = 50.0f; // 
   p->thermcal[1].max = 50.0f; // 
   p->thermcal[2].max = 50.0f; //    

   /* Positions installed set to 1. Otherwise 0. */
   p->thermcal[0].installed = 1; // GPIO 2 JP2
   p->thermcal[1].installed = 1; // GPIO 3 JP4
   p->thermcal[2].installed = 1; // GPIO 4 JP5

   /* Map thermistors. */
   p->tamb_idx  = 0;  // Ambient (inlet)
   p->tcell_idx = 1;  // Cell
   p->texit_idx = 2;  // Exit

   /* Fan temperature control parameters (deg C). */
   // Between max & min fan is proportional
   p->temp_fan_min  = 26.0f; // Ambient threshold
   p->temp_fan_max  = 48.0f; // Max: above this fan is 100%
   p->temp_fan_cell = 33.0f; // Tcell above this fan runs
   p->temp_fan_del  = 10.0f; // (Tcell - Tamb) > 0 enables fan
   p->temp_fan_min_pwm = 15; // Minimum pwm for this fan to run

   p->temp_fan_limit_hi = 44.0f; // Above this is no-launch range
   p->temp_fan_thres_hi = 38.0f; // Above this is caution zone
   p->temp_fan_thres_lo = 12.0f; // Below this is caution zone
   p->temp_fan_limit_lo =  8.0f; // Below this is no-launch range
   p->temp_fan_delta    =  4.0f; // Null zone beween Tamb and Tcell
   p->temp_fan_delay1   = 60;    // Time delay (secs) to improve ambient reading 

// List of CAN ID's for setting up hw filter for incoming msgs
   p->cid_uni_bms_emc1_i = CANID_UNI_BMS_EMC1_I;   // B0000000 UNIversal From EMC,  Incoming msg to BMS: X4=target CANID');   
   p->cid_uni_bms_emc2_i = CANID_UNI_BMS_EMC2_I;   // B0200000 UNIversal From EMC,  Incoming msg to BMS: X4=target CANID');   
   p->cid_uni_bms_pc_i   = CANID_UNI_BMS_PC_I;     // AEC00000 UNIversal From PC,   Incoming msg to BMS: X4=target CANID');   

// CAN ids BMS sends, others receive
   p->cid_msg_bms_cellvsmr = I_AM_CANID; // B0A00000
   return;
}
