GliderWinchItems/BMS/bmsmax14921/Ourtasks/adcbms.c

/******************************************************************************
* File Name          : adcbms.c
* Board              : bms14921: STM32L431
* Date First Issued  : 02/17/2022
* Description        : ADC management with MAX1421 board
*******************************************************************************/

/*
'MX ADC assignments 02/25/2022
Port Descript Chan'l sample scan order
PC1	FETCUR-rc	IN2	     47.5	1
PC3	FETCUR-A2	IN4	      2.5	2
PA0	OA INP	    IN5	     24.5	3
PA3	OA OUT	    IN8	     24.5	4
PA7	Hv-div1	    IN12	640.5	5
PC4	Therm 1	    IN13	247.5	6
PC5	Therm2	    IN14	247.5	7
Vref		    IN0	    247.5	8
Vtemp		    IN17	247.5	9
PA4	dcdc_15v	IN9	    247.5	10
PC0	BMS	        IN1 	 24.5	N/A
*/
#include "FreeRTOS.h"
#include "cmsis_os.h"
#include "malloc.h"
#include "adcbms.h"
#include "adcparams.h"
#include "ADCTask.h"
#include "main.h"
#include "DTW_counter.h"

#include "morse.h"

extern ADC_HandleTypeDef hadc1;
extern DMA_HandleTypeDef hdma_adc1;

extern SPI_HandleTypeDef hspi1;
extern DMA_HandleTypeDef hdma_spi1_rx;
extern DMA_HandleTypeDef hdma_spi1_tx;

extern TIM_HandleTypeDef htim15;

uint32_t dbdma1;
uint32_t dbdma2;
uint32_t dbadc1;
uint32_t dbadc2;



/* Save Hardware registers setup with 'MX for later restoration. */
static uint32_t adc_smpr1;
static uint32_t adc_sqr1; 
static uint32_t adc_cfgr; 
static uint32_t adc_cfgr2;

/* *************************************************************************
 * void adcbms_preinit(void);
 * @brief	: Save some things used later.
 * *************************************************************************/
 void adcbms_preinit(void)
{
	/* Change number of channels scanned to 10 (from 11) */
 	// MX & HAL initialization sets length of scan sequence 
 	// to 11 conversions but the 11th in the sequence is ADC_IN1 
 	// which is used for the BMS and not needed for this readout.
 	hadc1.Instance->SQR1 &= ~(0xF << 0); // Clear old value
 	hadc1.Instance->SQR1 |= (ADCDIRECTMAX << 0); // Insert new

	/* Save registers configured by 'MX for quick & easy restoration.
	   when reconfiguring from BMS to ADC scan mode.  */
 	adc_smpr1 = hadc1.Instance->SMPR1;
	adc_sqr1  = hadc1.Instance->SQR1;
	adc_cfgr  = hadc1.Instance->CFGR;
	adc_cfgr2 = hadc1.Instance->CFGR2;

	// Bit 0 DMAEN: Direct memory access enable. 1: DMA enabled
	// Bit 1 DMACFG: Direct memory access configuration 0: DMA One Shot mode selected
	adc_cfgr  |= 0x1;

	/* DMA1 CH1 peripheral and memory address: ADC */
	if ((hdma_adc1.Instance->CCR & 0x1) != 0) morse_trap(844);
	hdma_adc1.Instance->CPAR = (uint32_t)hadc1.Instance + 0x40;
	hdma_adc1.Instance->CMAR  =  (uint32_t)&adc1.dmabuf[0]; // DMA stores into this array

	/* DMA1 CH3 (SPI write) peripheral aand memory addresses: */
	hdma_spi1_tx.Instance->CPAR = (uint32_t)hspi1.Instance + 0x0C; // SPI DR adddress
	hdma_spi1_tx.Instance->CMAR = (uint32_t)&adcspiall.spitx24.uc[0]; // DMA stores from this array
//	hdma_spi1_tx.Instance->CCR |= (1 << 1); // TCIE: enable DMA interrupt

	/* DMA1 CH2 (SPI read) peripheral and memory addresses: */
	hdma_spi1_rx.Instance->CPAR = (uint32_t)hspi1.Instance + 0x0C; // SPI DR address
	hdma_spi1_rx.Instance->CMAR = (uint32_t)&adcspiall.spirx24.uc[0]; // DMA stores from this array

	/* TIM15 OC interrupt does nothing. */
	adcspiall.timstate = TIMSTATE_IDLE;

	/* MX may have these setup */
	hdma_spi1_tx.Instance->CCR &= ~0x2;  // Disable channel interrupt

	/* Make use of TIM15:CH1 OC for timing BMS delays. */
	// ARR default is 0xFFFF (max count-1)
	TIM15->SR = 0;          // Clear any interrupt flags
	TIM15->DIER = (1 << 1); // Bit 1 CC1IE: Capture/Compare 1 interrupt enable
	TIM15->CR1 |= 1; // Start counter

	/* Assure the MAX14921 is enabled. */
	// GPIOD PIN 2
	EN_GPIO_Port->BSRR = EN_Pin; // Set high.

	/* Set SMPL pin high and control sampling by /SMPL bit. */
	SELECT_GPIO_Port->BSRR = SELECT_Pin; // Set pin high

	// Bit 1 TXDMAEN: Tx buffer DMA enable
	// Bit 0 RXDMAEN: Rx buffer DMA enable
 	SPI1->CR2 |= (1<<1) | (1 << 0);

	// Bits 5:3 BR[2:0]: Baud rate control
 	SPI1->CR1 &= ~(0x7 << 3); // Clock divider
// 	SPI1->CR1 |=  (0x2 << 3); // 010: fPCLK /8
 	SPI1->CR1 |=  (0x1 << 3); // 010: fPCLK /4

// Bit 0 CPHA: Clock phase: 1: The second clock transition is the first data capture edge 	
 //SPI1->CR1 |=  (0x1 << 0);

	return;
}
/* *************************************************************************
 * void adcbms_config_adc(void);
 * @brief	: Set up for STM32L431 ADC readouts (excluding ADC used with MAX14921)
 * *************************************************************************/
 void adcbms_config_adc(void)
 {
 	struct ADCSPIALL* p = &adcspiall; // Convenience pointer

 	/* Skip most if already configured for ADC scan with DMA. */
 	if (p->config != 0)
 	{
	 	/* Here, either not initially configured or configured for BMS. */
	 	p->config = 0; // Show it is configured for DMA.

		// Cannot set registers if ADSTART is not 0.
	 	if ((hadc1.Instance->CR & (0x1 << 2)) != 0) morse_trap(850);

		/* ADC nterrupt */
		hadc1.Instance->IER &= ~0x7FF; // Clear all interrupt enables

		// Enable ADC
	 	hadc1.Instance->CR &= ~0x3F;
	// Debug: check bit config required to allow setting enable bit 	
	if ((hadc1.Instance->CR & (0x1 << 28)) == 0) morse_trap(867);
	//if ((hadc1.Instance->CR & 0x3F) != 0) morse_trap(866);

		hadc1.Instance->CR |= 0x1; // Enable

	 	/* Restore registers to 'MX & HAL initialized settings, saved in
	 	   'adcbms_preinit' (with SQR1 modified for 1 less channel in scan). */
		hadc1.Instance->SMPR1 = adc_smpr1;
		hadc1.Instance->SQR1  = adc_sqr1;
		hadc1.Instance->CFGR  = adc_cfgr;
		hadc1.Instance->CFGR2 = adc_cfgr2;
	}

	/* DMA_CNDTR: number of data to transfer register */
	// VERY IMPORTANT: DMA count be identical to ADC scan count. When the ADC
	// scan ends, the last store by the DMA must generate an interrupt. If the
	// DMA count is not zero, then where will be no interrupt.
	hdma_adc1.Instance->CNDTR  =  ADCDIRECTMAX;	// 

	/* DMA1 CH1 interrupt. */
	// DMA channel x configuration register (DMA_CCRx) */
	// Bit 0 EN: channel enable | Bit 1 TCIE: transfer complete interrupt enable
	hdma_adc1.Instance->CCR |= 0x3;

	return;
 }
/* *************************************************************************
 * void adcbms_config_bms(void);
 * @brief	: Set up for MAX14921 BMS cell readout
 * *************************************************************************/
 void adcbms_config_bms(void)
 {
	struct ADCSPIALL* p = &adcspiall; // Convenience pointer

	/* Set SMPL pin high and ontrol sampling by /SMPL bit. */
	SELECT_GPIO_Port->BSRR = SELECT_Pin; // Set pin high
//	SELECT_GPIO_Port->BSRR = SELECT_Pin<<16; // Set pin low

	/* Disable ADC DMA. */
	// Bit 1 TCIE: transfer complete interrupt enable
	// Bit 0 EN: channel enable
	hdma_adc1.Instance->CCR &= ~0x3;

 	// Bit 13 CONT: Single / continuous conversion mode for regular conversions
 	hadc1.Instance->CFGR &= ~(1 << 13); // Single conversion mode

	/* Setup ADC registers for cell readouts. */
 	// Cannot set registers if ADSTART is not 0.
 	if ((hadc1.Instance->CR & (0x1 << 2)) != 0) morse_trap(840);

  	/* Set oversample count */
  	 // Set: oversample enabled | oversample count = 16 | right shift count = 0;
//	hadc1.Instance->CFGR2 = ((0x1 << 0) | (0x3 << 2) | (0x0 << 5)); 
 	// Set: oversample enabled | oversample count = 32 | right shift count = 1;
	hadc1.Instance->CFGR2 = ((0x1 << 0) | (0x4 << 2) | (0x1 << 5)); 
	// Set: oversample enabled | oversample count = 64 | right shift count = 2;
 //	hadc1.Instance->CFGR2 = ((0x1 << 0) | (0x5 << 2) | (0x2 << 5)); 
	// Set: oversample enabled | oversample count = 128 | right shift count = 3;
// 	hadc1.Instance->CFGR2 = ((0x1 << 0) | (0x6 << 2) | (0x3 << 5)); 
	// Set: oversample enabled | oversample count = 256 | right shift count = 4;
 //	hadc1.Instance->CFGR2 = ((0x1 << 0) | (0x7 << 2) | (0x4 << 5)); 

 	// DMAEN: Direct memory access disable
 	// CONT:  Single conversion mode for regular conversions
	hadc1.Instance->CFGR = 0x80000000; // I think this is all that is needed!

	// Enable ADC interrupt
	// Bit 2 EOCIE: End of regular conversion interrupt enable
	// Bit 0 ADRDYIE: ADC ready interrupt enable
	hadc1.Instance->ISR = 0x7FF; // Clear all ADC interrupt flags
	hadc1.Instance->IER = (1 << 2); // Enable the one we want

	/* Set number of sampling cycles for first channel sequence. */
	hadc1.Instance->SMPR1 &= ~(0X7 << 0); // Clear old value
	hadc1.Instance->SMPR1 |=  (0X3 << 0); // 011: 24.5 ADC clock cycles
//	hadc1.Instance->SMPR1 |=  (0X4 << 0); // 100: 47.5 ADC clock cycles

 	/* Scan sequence. */
 	// Set Length of scan sequence to 1 conversion. (code = 0)
 	//   Bits 3:0 L[3:0]: Regular channel sequence length
 	// Set SQ1 (1st in sequence) to ADC_IN1 (code = 1)
 	//   Bits 10:6 SQ1[4:0]: 1st conversion in regular sequence
 	hadc1.Instance->SQR1 = (1 << 6); 

	p->config = 1; // Show ADC is configured for BMS.

	/* DMA1 CH2 CH3 interrupt enable. */
	// DMA channel x configuration register (DMA_CCRx) */
	// Bit 0 EN: channel enable | Bit 1 TCIE: transfer complete interrupt enable
	// Bit 8 GIF3: global interrupt flag for channel 3
//	*((uint32_t*)hdma_spi1_tx.Instance+0x8+(0x14 * 2) ) |= (1<<8);
//	hdma_spi1_tx.Instance->CCR  |= (1<<1);
//	hdma_spi1_rx.Instance->CCR  |= (1<<1);
	
	return;
 }
 
/* *************************************************************************
 * void adcbms_startreadbms(void);
 * @brief	: Set up and start a readout sequence
 * *************************************************************************/
 void adcbms_startreadbms(void)
 {
 	struct ADCSPIALL* p = &adcspiall; // Convenience pointer

 //	p->adcflag = 0; // ADC is idle
 	p->adcidx = 0; 

 	if (pssb->encycle == 1)
 	{
		EN_GPIO_Port->BSRR = EN_Pin<<16; // Set low.	
		p->timstate = TIMSTATE_IDLE; // Short delay for /CS pin
		EN_GPIO_Port->BSRR = EN_Pin; // Set high.
		osDelay(62); // Wait for flying caps to charge 
	}

 	p->timstate = TIMSTATE_IDLE; // JIC

 	// Save (for faster ISR use) 
 	p->updn = pssb->updn; //up/down cell readout order requested
// 	p->noverlap = pssb->noverlap; // not overlap spi with adc
 
 	// Configure ADC registers for BMS readout
 	adcbms_config_bms();

 	// Set /CS (GPIOA PIN_15) low to enable MAX14921.
	notCS_GPIO_Port->BSRR = (notCS_Pin<<16); // Reset: /CS set low

	// uc[0] = 0; uc[1] = 0; uc[2] = 0x04; uc[3] = not used;
		
	p->spitx24.uc[2] = 0x20; // /SMPL bit set high
//	p->spitx24.uc[2] = 0x00; // /SMPL bit set low

	/* Turn off discharge FETs during read. */
	p->spitx24.us[0] = 0;
	p->cellbitssave  = pssb->cellbits; // Save FET bits "locally"

//	SELECT_GPIO_Port->BSRR = SELECT_Pin<<16; // Set pin low
//	SELECT_GPIO_Port->BSRR = SELECT_Pin; // Set pin high
	
	/* Start transmission of command: set /SMPL bit high */
	// DMA_CNDTR: number of data to transfer register
//	hdma_spi1_rx.Instance->CCR &= ~1; // Disable channel
//	hdma_spi1_rx.Instance->CNDTR = 3; // Number to DMA transfer
//	hdma_spi1_rx.Instance->CCR |= 1;  // Enable channel

	hdma_spi1_tx.Instance->CCR &= ~1; // Disable channel
	hdma_spi1_tx.Instance->CNDTR = 3; // Number to DMA transfer
	hdma_spi1_tx.Instance->CCR |= 1;  // Enable channel 	

	// Bit 6 SPE: SPI enable
	SPI1->CR1 |= (1 << 6);	

// Debug
//extern uint32_t dbspidma;	
//dbspidma = DTWTIME;	
//osDelay(1000*400);

	// Set time duration for SPI to send 24b command
	TIM15->CCR1 = TIM15->CNT + SPIDELAY + 16; // Set SPI xmit duration

	// Set state for timer interrupt. (It will set a 50 us TIM2 delay to allow switch & settling.)
	p->timstate = TIMSTATE_SMPL; //

extern uint8_t dbisrflag;
dbisrflag = 1;	

extern uint32_t dbbms1;	
dbbms1 = DTWTIME;

dbdma1 = hdma_adc1.Instance->CCR; 
dbdma2 = hdma_adc1.Instance->CNDTR;
dbadc1 = hadc1.Instance->CR;
dbadc2 = hadc1.Instance->IER;
	// TIM15 interrupt will continue sequence.
	return;
 }

 
